dewayne57/GPSDO/Software/i2c.c

/*
 * Copyright (c) 2026, Dewayne L. Hafenstein.  All rights reserved.
 *
 * Bit-banging I2C implementation for PIC18F27Q43
 * Uses RC3 (SCL) and RC4 (SDA) with open drain configuration
 *
 * Licensed under the Apache License, Version 2.0 (the "License");
 * you may not use this file except in compliance with the License.
 * You may obtain a copy of the License at
 *   http://www.apache.org/licenses/LICENSE-2.0
 * Unless required by applicable law or agreed to in writing, software
 * distributed under the License is distributed on an "AS IS" BASIS,
 * WITHOUT WARRANTIES OR CONDITIONS OF ANY KIND, either express or implied.
 * See the License for the specific language governing permissions and
 * limitations under the License.
 *
 */
#include "i2c.h"
#include "config.h"
#include "faults.h"
#include <xc.h>

/****************************************************************************
 * Bit-banging I2C implementation for PIC18F27Q43
 * Uses RC3 (SCL) and RC4 (SDA) with open drain configuration
 ****************************************************************************/

// I2C timing delays for ~50kHz operation (more conservative)
#define I2C_DELAY() __delay_us(20)      // 20us delay for slower, more reliable timing
#define I2C_HALF_DELAY() __delay_us(10) // 10us half period delay

/****************************************************************************
 * forward define internal functions not exposed via i2c.h header file
 ****************************************************************************/
static void _i2cStart(void);
static void _i2cRestart(void);
static void _i2cStop(void);
static void _i2cSclHigh(void);
static void _i2cSclLow(void);
static void _i2cSdaHigh(void);
static void _i2cSdaLow(void);
static unsigned char _i2cSdaRead(void);
static unsigned char _i2cWriteByte(unsigned char data);
static unsigned char _i2cReadByte(unsigned char ack, unsigned char* value);

/****************************************************************************
 * PUBLIC API FUNCTIONS
 ****************************************************************************/

/****************************************************************************
 * Function: i2cWriteBuffer
 * Description: Write data to an I2C device
 * Parameters:
 *   address - The I2C device address
 *   data - Pointer to the data buffer to write
 *   length - The number of bytes to write
 * Returns: 0 on success, non-zero on failure
 * *************************************************************************/
unsigned char i2cWriteBuffer(unsigned char address, unsigned char* data, unsigned char length) {
    unsigned char i;
    unsigned char result;

    // Send start condition
    _i2cStart();

    // Send address with write bit (0)
    result = _i2cWriteByte((unsigned char)((address << 1) | 0x00));
    if (result != I2C_SUCCESS) {
        faultsAdd(FAULT_MSG_I2C_COMM_ERROR, FAULT_SEVERITY_ERROR);
        _i2cStop();
        return result;
    }

    // Send data bytes
    for (i = 0; i < length; i++) {
        result = _i2cWriteByte(data[i]);
        if (result != I2C_SUCCESS) {
            faultsAdd(FAULT_MSG_I2C_COMM_ERROR, FAULT_SEVERITY_ERROR);
            _i2cStop();
            return result;
        }
    }

    // Send stop condition
    _i2cStop();
    return I2C_SUCCESS;
}

/****************************************************************************
 * Function: i2cWriteRegister
 * Description: Write a single register on an I2C device.
 * Parameters:
 *   address - The I2C device address
 *   reg - The register address to write to
 *   data - The data byte to write
 * Returns: 0 on success, non-zero on failure
 * *************************************************************************/
unsigned char i2cWriteRegister(unsigned char address, unsigned char reg, unsigned char data) {
    unsigned char buffer[2];

    buffer[0] = reg;
    buffer[1] = data;
    return i2cWriteBuffer(address, buffer, 2);
}

/****************************************************************************
 * Function: i2cReadBuffer
 * Description: Read data from an I2C device
 * Parameters:
 *   address - The I2C device address
 *   data - Pointer to the data buffer to store the read data
 *   length - The number of bytes to read
 * Returns: 0 on success, non-zero on failure
 * *************************************************************************/
unsigned char i2cReadBuffer(unsigned char address, unsigned char* data, unsigned char length) {
    if (length == 0) {
        return I2C_SUCCESS;
    }

    unsigned char i;
    unsigned char result;

    // Send start condition
    _i2cStart();

    // Send address with read bit (1)
    result = _i2cWriteByte((unsigned char)((address << 1) | 0x01));
    if (result != I2C_SUCCESS) {
        faultsAdd(FAULT_MSG_I2C_COMM_ERROR, FAULT_SEVERITY_ERROR);
        _i2cStop();
        return result;
    }

    // Read data bytes
    for (i = 0; i < length; i++) {
        // ACK all bytes except the last one (NACK the last byte)
        result = _i2cReadByte(i < (length - 1), &data[i]);
        if (result != I2C_SUCCESS) {
            faultsAdd(FAULT_MSG_I2C_COMM_ERROR, FAULT_SEVERITY_ERROR);
            _i2cStop();
            return result;
        }
    }

    // Send stop condition
    _i2cStop();
    return I2C_SUCCESS;
}

/****************************************************************************
 * Function: i2cReadRegister
 * Description: Read a single register from an I2C device
 * Parameters:
 *   address - The I2C device address
 *   reg - The register address to read from
 *   data - Pointer to store the read data byte
 * Returns: 0 on success, non-zero on failure
 * *************************************************************************/
unsigned char i2cReadRegister(unsigned char address, unsigned char reg, unsigned char* data) {
    unsigned char result;

    // Send start condition
    _i2cStart();

    // Send address with write bit to write register address
    result = _i2cWriteByte((unsigned char)((address << 1) | 0x00));
    if (result != I2C_SUCCESS) {
        faultsAdd(FAULT_MSG_I2C_COMM_ERROR, FAULT_SEVERITY_ERROR);
        _i2cStop();
        return result;
    }

    // Send register address
    result = _i2cWriteByte(reg);
    if (result != I2C_SUCCESS) {
        faultsAdd(FAULT_MSG_I2C_COMM_ERROR, FAULT_SEVERITY_ERROR);
        _i2cStop();
        return result;
    }

    // Restart condition (maintains bus ownership)
    _i2cRestart();

    // Send address with read bit
    result = _i2cWriteByte((unsigned char)((address << 1) | 0x01));
    if (result != I2C_SUCCESS) {
        faultsAdd(FAULT_MSG_I2C_COMM_ERROR, FAULT_SEVERITY_ERROR);
        _i2cStop();
        return result;
    }

    // Read the data byte (NACK since it's the only/last byte)
    result = _i2cReadByte(0, data);
    if (result != I2C_SUCCESS) {
        faultsAdd(FAULT_MSG_I2C_COMM_ERROR, FAULT_SEVERITY_ERROR);
        _i2cStop();
        return result;
    }

    // Send stop condition
    _i2cStop();
    return I2C_SUCCESS;
}

/****************************************************************************
 * PRIVATE/INTERNAL FUNCTIONS
 ****************************************************************************/

void _i2cSclHigh(void) {
    TRISC |= SCL; // Release SCL (open drain - pull up will take it high)
    I2C_HALF_DELAY();
    __delay_us(2); // Additional delay for line to stabilize
}

void _i2cSclLow(void) {
    LATC &= ~SCL;  // Output low
    TRISC &= ~SCL; // Set as output
    I2C_HALF_DELAY();
}

void _i2cSdaHigh(void) {
    TRISC |= SDA; // Release SDA (open drain - pull up will take it high)
    I2C_HALF_DELAY();
    __delay_us(2); // Additional delay for line to stabilize
}

void _i2cSdaLow(void) {
    LATC &= ~SDA;  // Output low
    TRISC &= ~SDA; // Set as output
    I2C_HALF_DELAY();
}

unsigned char _i2cSdaRead(void) {
    TRISC |= SDA; // Ensure SDA is input
    I2C_HALF_DELAY();
    return PORTC & SDA; // Read SDA state
}

void _i2cStart(void) {
    // Start condition: SDA goes low while SCL is high
    _i2cSdaHigh(); // Ensure SDA is high
    _i2cSclHigh(); // Ensure SCL is high
    I2C_DELAY();
    _i2cSdaLow(); // SDA low while SCL high = START
    I2C_DELAY();
    _i2cSclLow(); // SCL low to complete start
}

void _i2cRestart(void) {
    // Restart condition: SDA goes high, then low while SCL is high
    // (without sending a stop first - maintains bus ownership)
    _i2cSdaHigh(); // SDA high first
    I2C_DELAY();
    _i2cSclHigh(); // SCL high
    I2C_DELAY();
    _i2cSdaLow(); // SDA low while SCL high = RESTART
    I2C_DELAY();
    _i2cSclLow(); // SCL low to complete restart
}

void _i2cStop(void) {
    // Stop condition: SDA goes high while SCL is high
    _i2cSdaLow(); // Ensure SDA is low
    I2C_DELAY();
    _i2cSclHigh(); // SCL high first
    I2C_DELAY();
    _i2cSdaHigh(); // SDA high while SCL high = STOP
    I2C_DELAY();
}

unsigned char _i2cWriteByte(unsigned char data) {
    unsigned char i;

    // Send 8 bits, MSB first
    for (i = 0; i < 8; i++) {
        if (data & 0x80) {
            _i2cSdaHigh();
        } else {
            _i2cSdaLow();
        }

        _i2cSclHigh(); // Clock the bit
        _i2cSclLow();
        data <<= 1;
    }

    // Check for ACK
    _i2cSdaHigh();                      // Release SDA for ACK
    _i2cSclHigh();                      // Clock the ACK bit
    unsigned char ack = !_i2cSdaRead(); // ACK is low
    _i2cSclLow();

    return ack ? I2C_SUCCESS : I2C_NACK;
}

unsigned char _i2cReadByte(unsigned char ack, unsigned char* value) {
    unsigned char data = 0;
    unsigned char i;

    _i2cSdaHigh(); // Release SDA for reading

    // Read 8 bits, MSB first
    for (i = 0; i < 8; i++) {
        data <<= 1;
        _i2cSclHigh();
        if (_i2cSdaRead()) {
            data |= 1;
        }
        _i2cSclLow();
    }

    // Send ACK/NACK
    if (ack) {
        _i2cSdaLow(); // ACK
    } else {
        _i2cSdaHigh(); // NACK
    }

    _i2cSclHigh();
    _i2cSclLow();

    *value = data;
    return I2C_SUCCESS;
}

/****************************************************************************
 * Function: i2cTestBusLines
 * Description: Test I2C bus lines for proper operation
 * Returns: 0 on success, non-zero on failure
 * *************************************************************************/
unsigned char i2cTestBusLines(void) {
    // Test SCL line
    _i2cSclLow();
    __delay_ms(1);
    if (PORTC & SCL) {
        return I2C_ERROR; // SCL should be low but reads high
    }

    _i2cSclHigh();
    __delay_ms(1);
    if (!(PORTC & SCL)) {
        return I2C_ERROR; // SCL should be high but reads low
    }

    // Test SDA line
    _i2cSdaLow();
    __delay_ms(1);
    if (PORTC & SDA) {
        return I2C_ERROR; // SDA should be low but reads high
    }

    _i2cSdaHigh();
    __delay_ms(1);
    if (!(PORTC & SDA)) {
        return I2C_ERROR; // SDA should be high but reads low
    }

    return I2C_SUCCESS;
}

/****************************************************************************
 * Function: i2cScanBus
 * Description: Scan I2C bus for responding devices
 * Returns: Number of devices found
 * *************************************************************************/
unsigned char i2cScanBus(unsigned char* found_addresses, unsigned char max_addresses) {
    unsigned char address;
    unsigned char found_count = 0;
    unsigned char result;

    for (address = 0x08; address < 0x78; address++) {
        // Skip reserved addresses
        if (address < 0x08 || address >= 0x78)
            continue;

        // Try to write to this address (just the address, no data)
        _i2cStart();
        result = _i2cWriteByte((unsigned char)((address << 1) | 0x00));
        _i2cStop();

        if (result == I2C_SUCCESS && found_count < max_addresses) {
            found_addresses[found_count] = address;
            found_count++;
        }

        // Small delay between attempts
        __delay_ms(1);
    }

    return found_count;
}

/****************************************************************************
 * End of i2c.c
 * **************************************************************************/
