dewayne57/GPSDO/Software/dac.c

/*
 * Copyright (c) 2026, Dewayne L. Hafenstein.  All rights reserved.
 *
 * Simple driver for a 16-bit I2C DAC (DAC8571 like device)
 * - Writes 16-bit values to the DAC via I2C
 * - Uses i2cWriteBuffer()
 *
 * Licensed under the Apache License, Version 2.0 (the "License");
 * you may not use this file except in compliance with the License.
 * You may obtain a copy of the License at
 *   http://www.apache.org/licenses/LICENSE-2.0
 * Unless required by applicable law or agreed to in writing, software
 * distributed under the License is distributed on an "AS IS" BASIS,
 * WITHOUT WARRANTIES OR CONDITIONS OF ANY KIND, either express or implied.
 * See the License for the specific language governing permissions and
 * limitations under the License.
 *
 */
#include "dac.h"
#include "config.h"
#include "i2c.h"
#include <stdint.h>
#include <xc.h>

static unsigned int dac_current = 0;
extern system_config_t system_config;
extern unsigned char i2c_buffer[I2C_BUFFER_SIZE];

/*
 * Initialize the DAC module.  Sets the DAC to a known state.
 */
void dac_init(void) {
    // If the system config contains a stored DAC value, use it as startup
    // Otherwise fall back to midpoint
    unsigned int start = DAC_MIDPOINT;
    if (system_config.magic == CONFIG_MAGIC && system_config.version == CONFIG_VERSION) {
        start = system_config.vco_dac;
        if (start >= DAC_RESOLUTION)
            start = DAC_RESOLUTION - 1U;
    }
    dac_current = start;
    dac_set_raw(dac_current);
}

/* DAC8571 write: control byte followed by 16-bit data (big-endian).
 * Control 0x10 = write-and-update, power-up (per DAC8571 datasheet).
 *
 * @param value  Raw DAC value to set (0..65535)
 * @return       None
 */
void dac_set_raw(unsigned int value) {
    if (value >= DAC_RESOLUTION)
        value = DAC_RESOLUTION - 1U;

    i2c_buffer[0] = 0x10;                                 // control: write + update DAC, power-up
    i2c_buffer[1] = (unsigned char)((value >> 8) & 0xFF); // D15..D8
    i2c_buffer[2] = (unsigned char)(value & 0xFF);        // D7..D0

    i2cWriteBuffer(DAC8571_ADDRESS, i2c_buffer, 3);
    dac_current = value;
}

/*
 * Get the current raw DAC value.
 *
 * @return Current DAC raw value (0..65535)
 */
unsigned int dac_get_raw(void) {
    return dac_current;
}
